alfishe/neogs/docs/_chips/sdcard-pinout.png

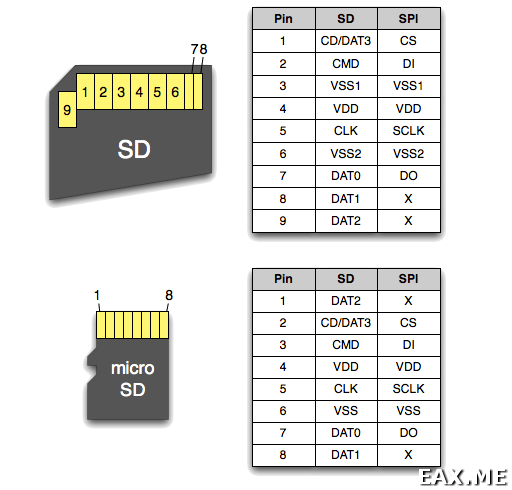
docs/_chips/sdcard-pinout.png
