alfishe/neogs/docs/photo/revC-VS/IMG_20250522_185837.jpg

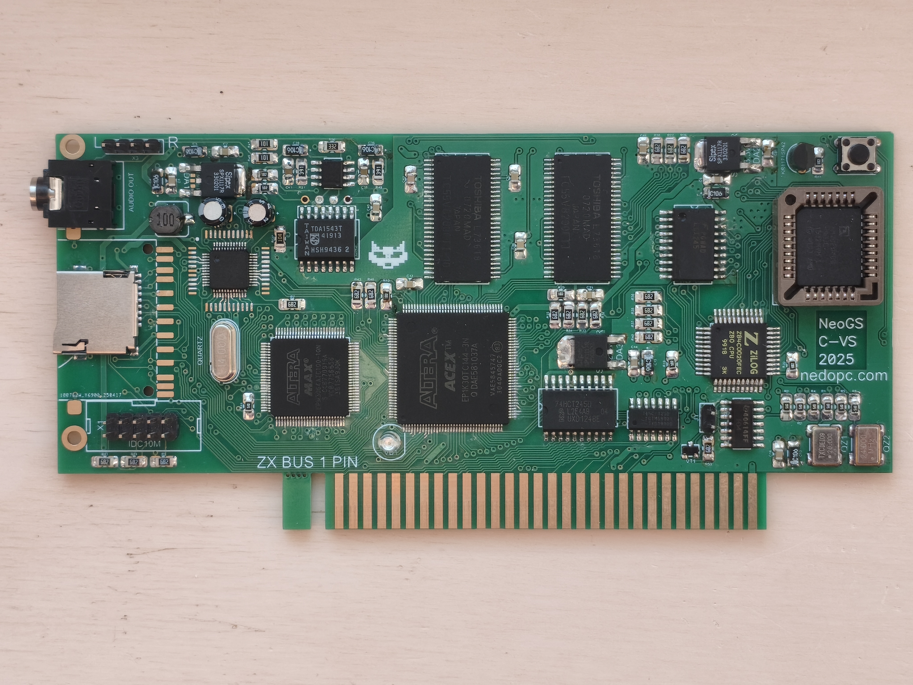
docs/photo/revC-VS/IMG_20250522_185837.jpg
