alfishe/neogs/docs/photo/revC-VS/IMG_20250522_185915.jpg

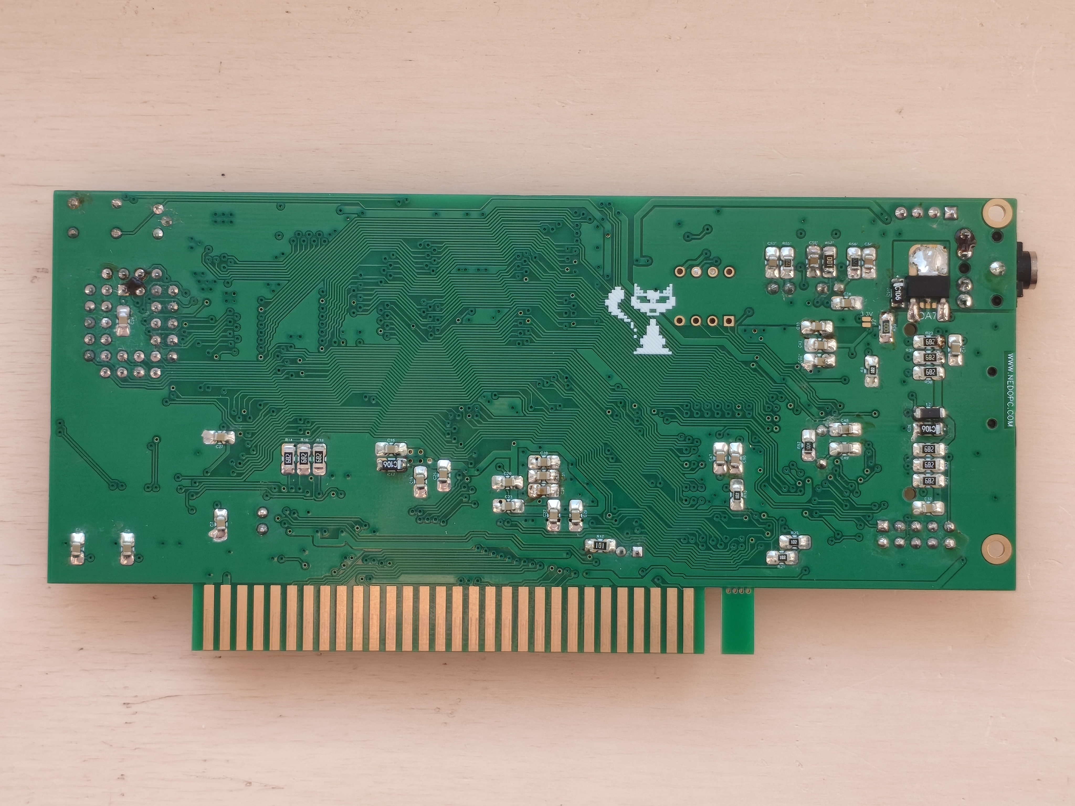
docs/photo/revC-VS/IMG_20250522_185915.jpg
