alfishe/neogs/fpga/current/common/spi2_modelled.png

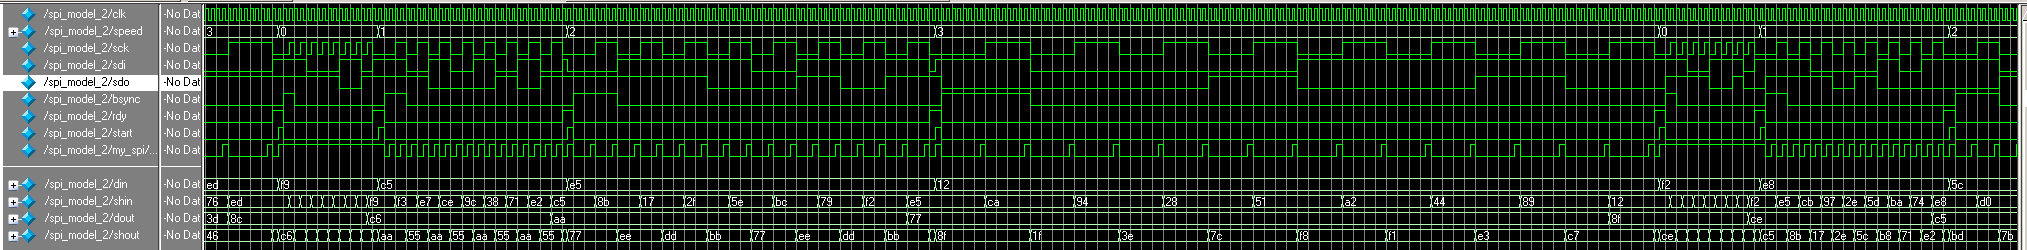
fpga/current/common/spi2_modelled.png
