alfishe/neogs/fpga/current/dma/dma_access.png

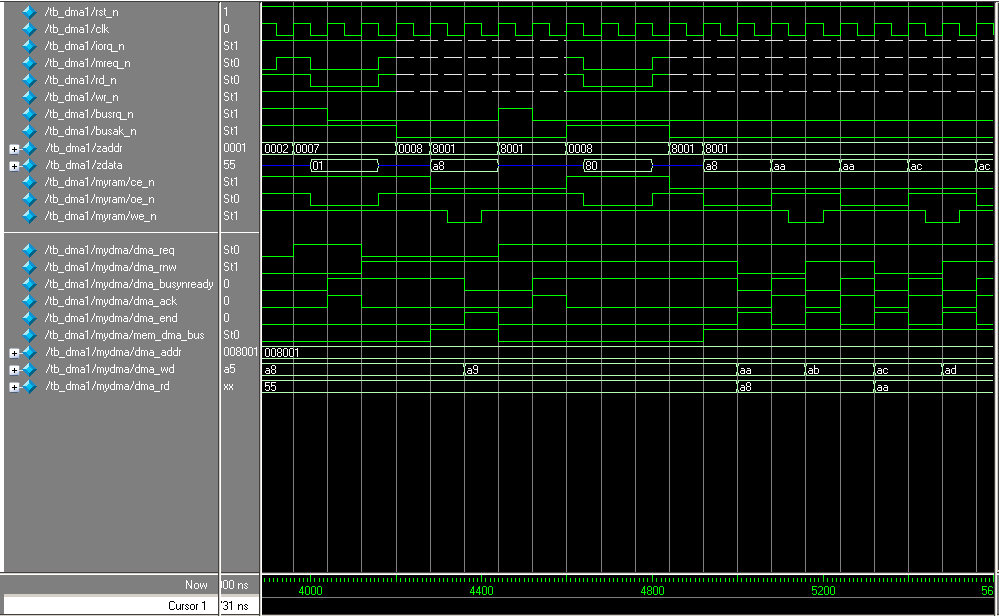
fpga/current/dma/dma_access.png
