alfishe/neogs/fpga/current/dma/modelsim/wave.bmp

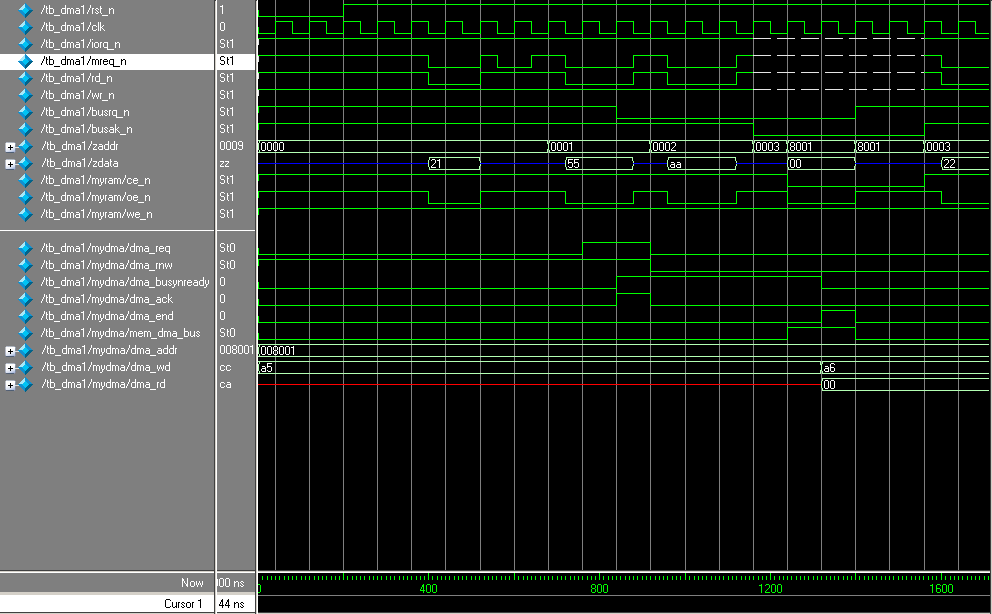
fpga/current/dma/modelsim/wave.bmp
